jcortade/despertador/images/IMG_20250628_172123.jpg

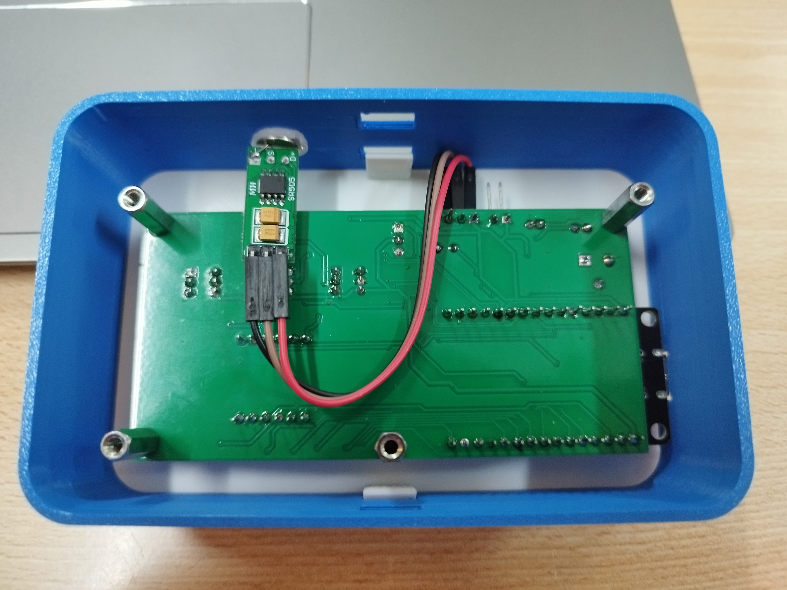
images/IMG_20250628_172123.jpg
